DrJonEA/RPIPico-RP2040Zero-Plugin/examples/Blink/src/RP2040-Plugin.h

/*
 * RP2040-Plugin.h
 *
 * Configuration of the Pico to RP2040 Pluging Zero
 *
 *  Created on: 25 Jan 2025
 *      Author: jondurrant
 */

#ifndef EXAMPLES_BLINK_RP2040_PLUGIN_H_
#define EXAMPLES_BLINK_RP2040_PLUGIN_H_

#define LED1 21
#define LED2 22




#endif /* EXAMPLES_BLINK_RP2040_PLUGIN_H_ */
